ademuri/open-motion-light/test/controller-test.cc

// Copyright 2024 Google LLC
//
// Licensed under the Apache License, Version 2.0 (the "License");
// you may not use this file except in compliance with the License.
// You may obtain a copy of the License at
//
//     http://www.apache.org/licenses/LICENSE-2.0
//
// Unless required by applicable law or agreed to in writing, software
// distributed under the License is distributed on an "AS IS" BASIS,
// WITHOUT WARRANTIES OR CONDITIONS OF ANY KIND, either express or implied.
// See the License for the specific language governing permissions and
// limitations under the License.

#include "controller.h"

#include <gtest/gtest.h>

#include <limits>

#include "fake-power-controller.h"
#include "fake-temperature-sensor.h"
#include "fake-vcnl4020.h"
#include "pb.h"
#include "pins.h"
#include "test-lib.h"
#include "types.h"

// Returns an analog value which approximates the millivolt reading. Note: due
// to precision limits, this is NOT exact.
uint16_t ComputeAnalogValueForMillivolts(uint32_t millivolts) {
  const uint32_t battery_millivolts = Controller::ReadRawBatteryMillivolts();
  EXPECT_LE(millivolts, battery_millivolts);
  return (millivolts * Controller::kAdcConfiguredMaxCount) / battery_millivolts;
}

TEST(ControllerTestFunctionsTest, ComputeAnalogValueForMillivolts) {
  const uint32_t pin = PA0;

  setAnalogRead(AVREF, kFakeVrefintCal * 0.75 / 4);
  const uint16_t battery_millivolts = 4000;
  ASSERT_EQ(Controller::ReadRawBatteryMillivolts(), battery_millivolts);

  const uint16_t value_1000 = ComputeAnalogValueForMillivolts(1000);
  setAnalogRead(pin, value_1000);
  EXPECT_EQ(Controller::ReadAnalogVoltageMillivolts(pin, battery_millivolts),
            1000);

  const uint16_t value_250 = ComputeAnalogValueForMillivolts(250);
  setAnalogRead(pin, value_250);
  EXPECT_EQ(Controller::ReadAnalogVoltageMillivolts(pin, battery_millivolts),
            250);
}

class ControllerTest : public LightTest {
 protected:
  void SetUp() override {
    LightTest::SetUp();
    controller.InitPins();
    setDigitalRead(kPinPowerAuto, true);
    setDigitalRead(kPinPowerOn, true);
    setDigitalRead(kPinBatteryNPowerGood, true);
    setDigitalRead(kPinBatteryStat, false);
    setDigitalRead(kPinMotionSensor, false);
    setDigitalRead(kPin5vDetect, false);
    setAnalogRead(kPinCc1, 0);
    setAnalogRead(kPinCc2, 0);

    // Set to 0 so that the light will always trigger in auto mode.
    vcnl4020.SetAmbient(0);

    // This yields a voltage of 3000 / 0.85 = 3529mV.
    setAnalogRead(AVREF, kFakeVrefintCal * 0.85 / 4);
    ASSERT_EQ(Controller::ReadRawBatteryMillivolts(), 3529);
  }

  FakeTemperatureSensor temperature_sensor;
  FakeVCNL4020 vcnl4020;
  FakePowerController power_controller;
  Controller controller{&temperature_sensor, &vcnl4020, &power_controller};
};

TEST_F(ControllerTest, Initializes) { EXPECT_TRUE(controller.Init()); }

TEST_F(ControllerTest, SetsPowerModeFromSwitch) {
  // These pins are inverted
  setDigitalRead(kPinPowerAuto, true);
  setDigitalRead(kPinPowerOn, true);

  ASSERT_TRUE(controller.Init());
  EXPECT_EQ(controller.GetPowerMode(), PowerMode::kOff);

  setDigitalRead(kPinPowerAuto, false);
  controller.Step();
  EXPECT_EQ(controller.GetPowerMode(), PowerMode::kAuto);

  setDigitalRead(kPinPowerOn, false);
  controller.Step();
  advanceMillis(11);
  controller.Step();
  EXPECT_EQ(controller.GetPowerMode(), PowerMode::kOn);

  setDigitalRead(kPinPowerAuto, true);
  advanceMillis(11);
  controller.Step();
  EXPECT_EQ(controller.GetPowerMode(), PowerMode::kOn);

  setDigitalRead(kPinPowerOn, true);
  advanceMillis(11);
  controller.Step();
  EXPECT_EQ(controller.GetPowerMode(), PowerMode::kOff);
}

TEST_F(ControllerTest, UpdatesLedWhenSwitchingModes) {
  setDigitalRead(kPinPowerAuto, true);
  setDigitalRead(kPinPowerOn, true);

  ASSERT_TRUE(controller.Init());
  const uint32_t duty_cycle = controller.GetLedDutyCycle();
  controller.Step();
  EXPECT_EQ(getAnalogWrite(kPinWhiteLed), 0);

  setDigitalRead(kPinPowerAuto, false);
  controller.Step();
  EXPECT_EQ(getAnalogWrite(kPinWhiteLed), duty_cycle);

  setDigitalRead(kPinPowerOn, false);
  advanceMillis(11);
  controller.Step();
  EXPECT_EQ(getAnalogWrite(kPinWhiteLed), duty_cycle);

  setDigitalRead(kPinPowerAuto, true);
  setDigitalRead(kPinPowerOn, true);
  advanceMillis(11);
  controller.Step();
  EXPECT_EQ(getAnalogWrite(kPinWhiteLed), 0);

  setDigitalRead(kPinMotionSensor, true);
  advanceMillis(11);
  controller.Step();
  EXPECT_EQ(getAnalogWrite(kPinWhiteLed), 0);

  setDigitalRead(kPinPowerAuto, false);
  setDigitalRead(kPinMotionSensor, false);
  advanceMillis(100);
  controller.Step();
  EXPECT_EQ(getAnalogWrite(kPinWhiteLed), duty_cycle)
      << "Switching to auto should turn on light";

  setDigitalRead(kPinPowerOn, false);
  advanceMillis(11);
  controller.Step();
  EXPECT_EQ(getAnalogWrite(kPinWhiteLed), duty_cycle);

  setDigitalRead(kPinPowerOn, true);
  advanceMillis(11);
  controller.Step();
  EXPECT_EQ(getAnalogWrite(kPinWhiteLed), duty_cycle);
}

TEST_F(ControllerTest, DebouncePowerMode) {
  setDigitalRead(kPinPowerAuto, true);
  setDigitalRead(kPinPowerOn, true);

  ASSERT_TRUE(controller.Init());
  ASSERT_EQ(controller.GetPowerMode(), PowerMode::kOff);

  setDigitalRead(kPinPowerAuto, false);
  controller.Step();
  ASSERT_EQ(controller.GetPowerMode(), PowerMode::kAuto);

  setDigitalRead(kPinPowerOn, false);
  controller.Step();
  EXPECT_EQ(controller.GetPowerMode(), PowerMode::kAuto);
  advanceMillis(10);
  controller.Step();
  EXPECT_EQ(controller.GetPowerMode(), PowerMode::kAuto);
  advanceMillis(1);
  controller.Step();
  EXPECT_EQ(controller.GetPowerMode(), PowerMode::kOn);

  setDigitalRead(kPinPowerOn, true);
  advanceMillis(10);
  controller.Step();
  EXPECT_EQ(controller.GetPowerMode(), PowerMode::kOn);
  advanceMillis(1);
  controller.Step();
  EXPECT_EQ(controller.GetPowerMode(), PowerMode::kAuto);
}

TEST_F(ControllerTest, MotionTriggersLed) {
  setDigitalRead(kPinPowerAuto, true);
  setDigitalRead(kPinPowerOn, true);

  ASSERT_TRUE(controller.Init());
  const uint32_t duty_cycle = controller.GetLedDutyCycle();
  ASSERT_GT(duty_cycle, 0);
  EXPECT_EQ(getAnalogWrite(kPinWhiteLed), 0);
  controller.Step();
  EXPECT_EQ(getAnalogWrite(kPinWhiteLed), 0);

  setDigitalRead(kPinPowerAuto, false);
  controller.Step();
  EXPECT_EQ(getAnalogWrite(kPinWhiteLed), duty_cycle);
  advanceMillis(controller.GetMotionTimeoutSeconds() * 1000);
  controller.Step();
  EXPECT_EQ(getAnalogWrite(kPinWhiteLed), duty_cycle);
  advanceMillis(10);
  controller.Step();
  EXPECT_EQ(getAnalogWrite(kPinWhiteLed), 0);

  setDigitalRead(kPinMotionSensor, true);
  controller.Step();
  EXPECT_EQ(getAnalogWrite(kPinWhiteLed), 0);
  advanceMillis(Controller::kMotionPulseLengthMs + 10);
  controller.Step();
  EXPECT_EQ(getAnalogWrite(kPinWhiteLed), duty_cycle);
  setDigitalRead(kPinMotionSensor, false);

  advanceMillis(10);
  controller.Step();
  EXPECT_EQ(getAnalogWrite(kPinWhiteLed), duty_cycle);

  advanceMillis(controller.GetMotionTimeoutSeconds() * 1000 - 10);
  controller.Step();
  EXPECT_EQ(getAnalogWrite(kPinWhiteLed), duty_cycle);

  advanceMillis(1);
  controller.Step();
  EXPECT_EQ(getAnalogWrite(kPinWhiteLed), 0);
}

TEST_F(ControllerTest, ContinuedMotionKeepsLedOn) {
  setDigitalRead(kPinPowerAuto, false);
  setDigitalRead(kPinPowerOn, true);
  setDigitalRead(kPinMotionSensor, false);

  ASSERT_TRUE(controller.Init());
  const uint32_t duty_cycle = controller.GetLedDutyCycle();
  ASSERT_GT(duty_cycle, 0);
  EXPECT_EQ(getAnalogWrite(kPinWhiteLed), 0);
  controller.Step();
  EXPECT_EQ(getAnalogWrite(kPinWhiteLed), duty_cycle);

  advanceMillis(controller.GetMotionTimeoutSeconds() * 1000 + 10);
  controller.Step();
  EXPECT_EQ(getAnalogWrite(kPinWhiteLed), 0);

  setDigitalRead(kPinMotionSensor, true);
  advanceMillis(Controller::kMotionPulseLengthMs);
  controller.Step();
  EXPECT_EQ(getAnalogWrite(kPinWhiteLed), 0);

  advanceMillis(10);
  controller.Step();
  EXPECT_EQ(getAnalogWrite(kPinWhiteLed), duty_cycle);
  setDigitalRead(kPinMotionSensor, false);

  advanceMillis(10);
  controller.Step();
  EXPECT_EQ(getAnalogWrite(kPinWhiteLed), duty_cycle);

  advanceMillis(controller.GetMotionTimeoutSeconds() * 1000 - 20);
  controller.Step();
  EXPECT_EQ(getAnalogWrite(kPinWhiteLed), duty_cycle);

  setDigitalRead(kPinMotionSensor, true);
  advanceMillis(1);
  controller.Step();
  EXPECT_EQ(getAnalogWrite(kPinWhiteLed), duty_cycle);
  advanceMillis(controller.GetMotionTimeoutSeconds() * 1000 * 10);
  controller.Step();
  EXPECT_EQ(getAnalogWrite(kPinWhiteLed), duty_cycle);

  setDigitalRead(kPinMotionSensor, false);
  advanceMillis(controller.GetMotionTimeoutSeconds() * 1000);
  controller.Step();
  EXPECT_EQ(getAnalogWrite(kPinWhiteLed), duty_cycle);
  advanceMillis(1);
  controller.Step();
  EXPECT_EQ(getAnalogWrite(kPinWhiteLed), 0);
}

TEST_F(ControllerTest, ReadsBatteryVoltage) {
  ASSERT_TRUE(controller.Init());

  setAnalogRead(AVREF, kFakeVrefintCal / 4);
  EXPECT_EQ(Controller::ReadRawBatteryMillivolts(), 3000);

  setAnalogRead(AVREF, kFakeVrefintCal * 0.75 / 4);
  EXPECT_EQ(Controller::ReadRawBatteryMillivolts(), 4000);

  setAnalogRead(AVREF, kFakeVrefintCal * 1.5 / 4);
  EXPECT_EQ(Controller::ReadRawBatteryMillivolts(), 2000);
}

TEST_F(ControllerTest, FiltersBatteryVoltage) {
  setAnalogRead(AVREF, kFakeVrefintCal / 4);

  ASSERT_TRUE(controller.Init());
  ASSERT_EQ(Controller::ReadRawBatteryMillivolts(), 3000);
  EXPECT_EQ(controller.GetFilteredBatteryMillivolts(), 3000);

  advanceMillis(Controller::kBatteryFilterRunIntervalMillis + 1);
  controller.Step();
  EXPECT_EQ(controller.GetFilteredBatteryMillivolts(), 3000);

  advanceMillis(Controller::kBatteryFilterRunIntervalMillis + 1);
  setAnalogRead(AVREF, kFakeVrefintCal * 0.75 / 4);
  ASSERT_EQ(Controller::ReadRawBatteryMillivolts(), 4000);
  controller.Step();
  EXPECT_GE(controller.GetFilteredBatteryMillivolts(), 3000);
  EXPECT_LT(controller.GetFilteredBatteryMillivolts(), 4000);

  for (uint32_t n = 0; n < (256 / Controller::kBatteryFilterAlpha) * 2; n++) {
    advanceMillis(Controller::kBatteryFilterRunIntervalMillis + 1);
    controller.Step();
    EXPECT_GE(controller.GetFilteredBatteryMillivolts(), 3000) << "step " << n;
    EXPECT_LT(controller.GetFilteredBatteryMillivolts(), 4000) << "step " << n;
  }
  EXPECT_GT(controller.GetFilteredBatteryMillivolts(), 3800);
}

TEST_F(ControllerTest, SetsPowerStatus) {
  setDigitalRead(kPinBatteryNPowerGood, true);
  setDigitalRead(kPinBatteryStat, false);
  setAnalogRead(kPinCc1, ComputeAnalogValueForMillivolts(0));

  ASSERT_TRUE(controller.Init());
  EXPECT_EQ(controller.GetPowerStatus(), PowerStatus::kBattery);
  controller.Step();
  EXPECT_EQ(controller.GetPowerStatus(), PowerStatus::kBattery);

  setDigitalRead(kPinBatteryNPowerGood, false);
  controller.Step();
  EXPECT_EQ(controller.GetPowerStatus(), PowerStatus::kCharging);

  setDigitalRead(kPinBatteryStat, true);
  controller.Step();
  EXPECT_EQ(controller.GetPowerStatus(), PowerStatus::kCharged);

  // TODO: add test coverage for charge error, once that functionality is
  // implemented.
}

TEST_F(ControllerTest, UsesHysteresisForBatteryVoltage) {
  setAnalogRead(AVREF, kFakeVrefintCal * 1.5 / 4);
  ASSERT_EQ(controller.ReadRawBatteryMillivolts(), 2000);

  ASSERT_TRUE(controller.Init());
  EXPECT_EQ(controller.GetPowerStatus(), PowerStatus::kBattery);
  controller.Step();
  ASSERT_EQ(controller.GetFilteredBatteryMillivolts(), 2000);
  EXPECT_EQ(controller.GetPowerStatus(), PowerStatus::kLowBatteryCutoff);

  setAnalogRead(AVREF, kFakeVrefintCal / 1.05 / 4);
  ASSERT_EQ(controller.ReadRawBatteryMillivolts(), 3157);

  for (uint32_t t = 0; t < 100; t++) {
    advanceMillis(100);
    controller.Step();
    EXPECT_EQ(controller.GetPowerStatus(), PowerStatus::kLowBatteryCutoff);
  }

  ASSERT_EQ(controller.GetFilteredBatteryMillivolts(), 3157);
  EXPECT_EQ(controller.GetPowerStatus(), PowerStatus::kLowBatteryCutoff);

  setAnalogRead(AVREF, kFakeVrefintCal / 1.1 / 4);
  ASSERT_EQ(controller.ReadRawBatteryMillivolts(), 3305);

  for (uint32_t t = 0; t < 100; t++) {
    advanceMillis(100);
    controller.Step();
  }
  ASSERT_EQ(controller.GetFilteredBatteryMillivolts(), 3305);
  EXPECT_EQ(controller.GetPowerStatus(), PowerStatus::kBattery);

  setAnalogRead(AVREF, kFakeVrefintCal / 1.05 / 4);
  ASSERT_EQ(controller.ReadRawBatteryMillivolts(), 3157);

  for (uint32_t t = 0; t < 100; t++) {
    advanceMillis(100);
    controller.Step();
    EXPECT_EQ(controller.GetPowerStatus(), PowerStatus::kBattery);
  }

  ASSERT_EQ(controller.GetFilteredBatteryMillivolts(), 3157);
  EXPECT_EQ(controller.GetPowerStatus(), PowerStatus::kBattery);
}

TEST_F(ControllerTest, DetectsLowBatteryVoltage) {
  setDigitalRead(kPinBatteryNPowerGood, true);
  setDigitalRead(kPinBatteryStat, false);

  setAnalogRead(AVREF, kFakeVrefintCal * 1.5 / 4);
  ASSERT_EQ(controller.ReadRawBatteryMillivolts(), 2000);

  ASSERT_TRUE(controller.Init());
  EXPECT_EQ(controller.GetPowerStatus(), PowerStatus::kBattery);
  controller.Step();
  ASSERT_EQ(controller.GetFilteredBatteryMillivolts(), 2000);
  EXPECT_EQ(controller.GetPowerStatus(), PowerStatus::kLowBatteryCutoff);

  setDigitalRead(kPinBatteryNPowerGood, false);
  controller.Step();
  EXPECT_EQ(controller.GetPowerStatus(),
            PowerStatus::kLowBatteryCutoffCharging);

  setDigitalRead(kPinBatteryStat, true);
  controller.Step();
  EXPECT_EQ(controller.GetPowerStatus(), PowerStatus::kLowBatteryCutoff);
}

TEST_F(ControllerTest, DoesntTurnOnLedWhenBatteryLow) {
  setAnalogRead(AVREF, kFakeVrefintCal * 1.5 / 4);
  ASSERT_EQ(controller.ReadRawBatteryMillivolts(), 2000);

  ASSERT_TRUE(controller.Init());
  ASSERT_EQ(controller.GetPowerStatus(), PowerStatus::kBattery);
  controller.Step();
  ASSERT_EQ(controller.GetFilteredBatteryMillivolts(), 2000);
  ASSERT_EQ(controller.GetPowerStatus(), PowerStatus::kLowBatteryCutoff);

  setDigitalRead(kPinPowerOn, LOW);
  advanceMillis(100);
  controller.Step();
  EXPECT_EQ(controller.GetPowerMode(), PowerMode::kOn);
  EXPECT_EQ(getDigitalWrite(kPinWhiteLed), 0);
  EXPECT_EQ(getAnalogWrite(kPinBatteryLed1), 0);
  EXPECT_EQ(getAnalogWrite(kPinBatteryLed2), 0);
  EXPECT_EQ(getAnalogWrite(kPinBatteryLed3), 0);

  setDigitalRead(kPinPowerOn, HIGH);
  setDigitalRead(kPinPowerAuto, LOW);
  advanceMillis(100);
  controller.Step();
  EXPECT_EQ(controller.GetPowerMode(), PowerMode::kAuto);
  EXPECT_EQ(getDigitalWrite(kPinWhiteLed), 0);
  EXPECT_EQ(getAnalogWrite(kPinBatteryLed1), 0);
  EXPECT_EQ(getAnalogWrite(kPinBatteryLed2), 0);
  EXPECT_EQ(getAnalogWrite(kPinBatteryLed3), 0);

  setAnalogRead(kPinCc1, ComputeAnalogValueForMillivolts(1800));
  setDigitalRead(kPinBatteryNPowerGood, false);
  setDigitalRead(kPinBatteryStat, false);
  controller.Step();
  ASSERT_EQ(controller.GetUSBStatus(), USBStatus::kUSB3_0);
  ASSERT_EQ(controller.GetPowerStatus(),
            PowerStatus::kLowBatteryCutoffCharging);
  EXPECT_EQ(getDigitalWrite(kPinWhiteLed), 0);
}

TEST_F(ControllerTest, TurnsOffLedWhenBatteryLow) {
  ASSERT_TRUE(controller.Init());
  ASSERT_EQ(controller.GetUSBStatus(), USBStatus::kNoConnection);
  ASSERT_EQ(controller.GetPowerStatus(), PowerStatus::kBattery);
  controller.Step();
  ASSERT_GT(controller.GetFilteredBatteryMillivolts(),
            Controller::kBatteryVoltage1);
  ASSERT_EQ(controller.GetUSBStatus(), USBStatus::kNoConnection);
  ASSERT_EQ(controller.GetPowerStatus(), PowerStatus::kBattery);

  setDigitalRead(kPinPowerOn, LOW);
  advanceMillis(100);
  controller.Step();
  EXPECT_EQ(controller.GetPowerMode(), PowerMode::kOn);
  EXPECT_EQ(getAnalogWrite(kPinWhiteLed), controller.GetLedDutyCycle());
  EXPECT_EQ(getAnalogWrite(kPinBatteryLed1),
            Controller::kBatteryLedActiveBrightness);
  EXPECT_EQ(getAnalogWrite(kPinBatteryLed2),
            Controller::kBatteryLedActiveBrightness);
  EXPECT_EQ(getAnalogWrite(kPinBatteryLed3),
            Controller::kBatteryLedActiveBrightness);

  setAnalogRead(AVREF, kFakeVrefintCal * 1.5 / 4);
  ASSERT_EQ(controller.ReadRawBatteryMillivolts(), 2000);

  for (uint32_t t = 0; t < 10; t++) {
    advanceMillis(100);
    controller.Step();
  }

  ASSERT_LT(controller.GetFilteredBatteryMillivolts(),
            Controller::kBatteryVoltage0);
  EXPECT_EQ(controller.GetPowerStatus(), PowerStatus::kLowBatteryCutoff);
  EXPECT_EQ(controller.GetPowerMode(), PowerMode::kOn);
  EXPECT_EQ(getAnalogWrite(kPinWhiteLed), 0);
  EXPECT_EQ(getAnalogWrite(kPinBatteryLed1), 0);
  EXPECT_EQ(getAnalogWrite(kPinBatteryLed2), 0);
  EXPECT_EQ(getAnalogWrite(kPinBatteryLed3), 0);
}

TEST_F(ControllerTest, SetsUSBStatus) {
  // Battery voltage should be max ~3.6V.
  setAnalogRead(AVREF, kFakeVrefintCal * 0.8 / 4);
  ASSERT_EQ(Controller::ReadRawBatteryMillivolts(), 3750);

  const uint16_t vusb_min = ComputeAnalogValueForMillivolts(200);
  const uint16_t vusb_max = ComputeAnalogValueForMillivolts(610);
  const uint16_t v1_5_min = ComputeAnalogValueForMillivolts(700);
  const uint16_t v1_5_max = ComputeAnalogValueForMillivolts(1160);
  const uint16_t v3_0_min = ComputeAnalogValueForMillivolts(1310);
  const uint16_t v3_0_max = ComputeAnalogValueForMillivolts(2040);
  setAnalogRead(kPinCc1, 0);
  setAnalogRead(kPinCc2, 0);

  ASSERT_TRUE(controller.Init());
  EXPECT_EQ(controller.GetUSBStatus(), USBStatus::kNoConnection);
  controller.Step();
  EXPECT_EQ(controller.GetUSBStatus(), USBStatus::kNoConnection);
  EXPECT_FALSE(getDigitalWrite(kPinChargeHighCurrentEnable));

  setAnalogRead(kPinCc1, vusb_min - 1);
  controller.Step();
  EXPECT_EQ(controller.GetUSBStatus(), USBStatus::kNoConnection);
  EXPECT_FALSE(getDigitalWrite(kPinChargeHighCurrentEnable));

  setAnalogRead(kPinCc1, vusb_min + 1);
  controller.Step();
  EXPECT_EQ(controller.GetUSBStatus(), USBStatus::kStandardUsb);
  EXPECT_FALSE(getDigitalWrite(kPinChargeHighCurrentEnable));

  setAnalogRead(kPinCc1, vusb_max - 1);
  controller.Step();
  EXPECT_EQ(controller.GetUSBStatus(), USBStatus::kStandardUsb);
  EXPECT_FALSE(getDigitalWrite(kPinChargeHighCurrentEnable));

  setAnalogRead(kPinCc1, v1_5_min + 1);
  controller.Step();
  EXPECT_EQ(controller.GetUSBStatus(), USBStatus::kUSB1_5);
  EXPECT_TRUE(getDigitalWrite(kPinChargeHighCurrentEnable));

  setAnalogRead(kPinCc1, v1_5_max - 1);
  controller.Step();
  EXPECT_EQ(controller.GetUSBStatus(), USBStatus::kUSB1_5);
  EXPECT_TRUE(getDigitalWrite(kPinChargeHighCurrentEnable));

  setAnalogRead(kPinCc1, v3_0_min + 1);
  controller.Step();
  EXPECT_EQ(controller.GetUSBStatus(), USBStatus::kUSB3_0);
  EXPECT_TRUE(getDigitalWrite(kPinChargeHighCurrentEnable));

  setAnalogRead(kPinCc1, v3_0_max - 1);
  controller.Step();
  EXPECT_EQ(controller.GetUSBStatus(), USBStatus::kUSB3_0);
  EXPECT_TRUE(getDigitalWrite(kPinChargeHighCurrentEnable));
}

TEST_F(ControllerTest, SetsUSBFromCC1AndCC2) {
  // Battery voltage should be max ~3.6V.
  setAnalogRead(AVREF, kFakeVrefintCal * 0.8 / 4);
  ASSERT_EQ(Controller::ReadRawBatteryMillivolts(), 3750);

  const uint16_t vusb_max = ComputeAnalogValueForMillivolts(610);
  const uint16_t v1_5_min = ComputeAnalogValueForMillivolts(700);
  setAnalogRead(kPinCc1, 0);
  setAnalogRead(kPinCc2, 0);

  ASSERT_TRUE(controller.Init());
  controller.Step();
  ASSERT_EQ(controller.GetUSBStatus(), USBStatus::kNoConnection);
  EXPECT_FALSE(getDigitalWrite(kPinChargeHighCurrentEnable));

  setAnalogRead(kPinCc1, v1_5_min + 1);
  controller.Step();
  EXPECT_EQ(controller.GetUSBStatus(), USBStatus::kUSB1_5);
  EXPECT_TRUE(getDigitalWrite(kPinChargeHighCurrentEnable));

  setAnalogRead(kPinCc1, 0);
  setAnalogRead(kPinCc2, v1_5_min + 1);
  controller.Step();
  EXPECT_EQ(controller.GetUSBStatus(), USBStatus::kUSB1_5);
  EXPECT_TRUE(getDigitalWrite(kPinChargeHighCurrentEnable));

  setAnalogRead(kPinCc1, vusb_max - 1);
  setAnalogRead(kPinCc2, v1_5_min + 1);
  controller.Step();
  EXPECT_EQ(controller.GetUSBStatus(), USBStatus::kUSB1_5);
  EXPECT_TRUE(getDigitalWrite(kPinChargeHighCurrentEnable));
}

TEST_F(ControllerTest, DoesntTurnOnWhenUSBConnected) {
  const uint16_t vusb_max = ComputeAnalogValueForMillivolts(610);
  setAnalogRead(kPinCc1, vusb_max);
  setAnalogRead(kPinCc2, 0);

  ASSERT_TRUE(controller.Init());
  controller.Step();
  ASSERT_EQ(controller.GetUSBStatus(), USBStatus::kStandardUsb);

  setDigitalRead(kPinPowerOn, false);
  controller.Step();
  ASSERT_EQ(controller.GetPowerMode(), PowerMode::kOn);
  EXPECT_EQ(getAnalogWrite(kPinWhiteLed), 0);

  setAnalogRead(kPinCc1, 0);
  controller.Step();
  ASSERT_EQ(controller.GetUSBStatus(), USBStatus::kNoConnection);
  EXPECT_EQ(getAnalogWrite(kPinWhiteLed), controller.GetLedDutyCycle());

  setAnalogRead(kPinCc1, vusb_max);
  controller.Step();
  ASSERT_EQ(controller.GetUSBStatus(), USBStatus::kStandardUsb);
  EXPECT_EQ(getAnalogWrite(kPinWhiteLed), 0);

  setDigitalRead(kPinPowerOn, true);
  setDigitalRead(kPinPowerAuto, false);
  advanceMillis(11);
  controller.Step();
  ASSERT_EQ(controller.GetPowerMode(), PowerMode::kAuto);
  EXPECT_EQ(getAnalogWrite(kPinWhiteLed), 0);

  setAnalogRead(kPinCc1, 0);
  setDigitalRead(kPinMotionSensor, true);
  controller.Step();
  ASSERT_EQ(controller.GetUSBStatus(), USBStatus::kNoConnection);
  EXPECT_EQ(getAnalogWrite(kPinWhiteLed), controller.GetLedDutyCycle());

  setAnalogRead(kPinCc1, vusb_max);
  controller.Step();
  ASSERT_EQ(controller.GetUSBStatus(), USBStatus::kStandardUsb);
  EXPECT_EQ(getAnalogWrite(kPinWhiteLed), 0);
}

TEST_F(ControllerTest, ReadsAnalogVoltage) {
  const uint32_t pin = PA0;
  pinMode(pin, INPUT_ANALOG);

  setAnalogRead(pin, Controller::kAdcConfiguredMaxCount);
  EXPECT_EQ(
      Controller::ReadAnalogVoltageMillivolts(pin, /*battery_millivolts=*/3000),
      3000);

  setAnalogRead(pin, Controller::kAdcConfiguredMaxCount / 2);
  EXPECT_EQ(
      Controller::ReadAnalogVoltageMillivolts(pin, /*battery_millivolts=*/3000),
      1500);
}

std::array<uint32_t, 3> BatteryLeds(uint32_t led1, uint32_t led2,
                                    uint32_t led3) {
  return {led1, led2, led3};
}

std::array<uint32_t, 3> GetBatteryLeds() {
  return BatteryLeds(getAnalogWrite(kPinBatteryLed1),
                     getAnalogWrite(kPinBatteryLed2),
                     getAnalogWrite(kPinBatteryLed3));
}

TEST_F(ControllerTest, DisplaysBatteryVoltage) {
  setDigitalRead(kPinBatteryNPowerGood, true);
  setDigitalRead(kPinBatteryStat, false);

  setAnalogRead(AVREF,
                (kFakeVrefintCal * Controller::kReferenceSupplyMillivolts) /
                    (Controller::kBatteryVoltage1 + 100) / 4);
  ASSERT_GT(controller.ReadRawBatteryMillivolts(),
            Controller::kBatteryVoltage1);
  ASSERT_TRUE(controller.Init());
  EXPECT_EQ(GetBatteryLeds(), BatteryLeds(0, 0, 0));

  setDigitalRead(kPinPowerAuto, false);
  controller.Step();
  ASSERT_EQ(controller.GetPowerMode(), PowerMode::kAuto);
  EXPECT_EQ(GetBatteryLeds(),
            BatteryLeds(Controller::kBatteryLedActiveBrightness,
                        Controller::kBatteryLedActiveBrightness,
                        Controller::kBatteryLedActiveBrightness));

  advanceMillis(Controller::kBatteryLevelDisplayTimeSeconds * 1000 + 10);
  controller.Step();
  EXPECT_EQ(GetBatteryLeds(), BatteryLeds(0, 0, 0));

  // Medium voltage
  setAnalogRead(AVREF,
                (kFakeVrefintCal * Controller::kReferenceSupplyMillivolts) /
                    (Controller::kBatteryVoltage0 + 10) / 4);
  ASSERT_GT(controller.ReadRawBatteryMillivolts(),
            Controller::kBatteryVoltage0);
  ASSERT_LT(controller.ReadRawBatteryMillivolts(),
            Controller::kBatteryVoltage1);
  // Pump the battery voltage filters
  for (uint32_t n = 0; n < 100; n++) {
    advanceMillis(Controller::kBatteryFilterRunIntervalMillis + 1);
    controller.Step();
  }

  setDigitalRead(kPinPowerAuto, true);
  setDigitalRead(kPinPowerOn, false);
  controller.Step();
  ASSERT_EQ(controller.GetPowerMode(), PowerMode::kOn);
  EXPECT_EQ(GetBatteryLeds(),
            BatteryLeds(Controller::kBatteryLedPlaceholderBrightness,
                        Controller::kBatteryLedActiveBrightness,
                        Controller::kBatteryLedActiveBrightness));

  // Low voltage
  setAnalogRead(AVREF,
                (kFakeVrefintCal * Controller::kReferenceSupplyMillivolts) /
                    (Controller::kBatteryVoltage0 - 10) / 4);
  ASSERT_LT(controller.ReadRawBatteryMillivolts(),
            Controller::kBatteryVoltage0);
  // Pump the battery voltage filters
  for (uint32_t n = 0; n < 100; n++) {
    advanceMillis(Controller::kBatteryFilterRunIntervalMillis + 1);
    controller.Step();
  }

  setDigitalRead(kPinPowerAuto, false);
  setDigitalRead(kPinPowerOn, true);
  controller.Step();
  ASSERT_EQ(controller.GetPowerMode(), PowerMode::kAuto);
  EXPECT_EQ(GetBatteryLeds(),
            BatteryLeds(Controller::kBatteryLedPlaceholderBrightness,
                        Controller::kBatteryLedPlaceholderBrightness,
                        Controller::kBatteryLedActiveBrightness));
}

TEST_F(ControllerTest, AmbientAndProximitySensorsWork) {
  ASSERT_TRUE(controller.Init());

  vcnl4020.SetAmbient(500);
  EXPECT_EQ(controller.ReadAmbientLight(), 500);

  vcnl4020.SetProximity(600);
  EXPECT_EQ(controller.ReadProximity(), 600);
}

TEST_F(ControllerTest, Sleeps) {
  ASSERT_TRUE(controller.Init());
  EXPECT_EQ(controller.GetPowerMode(), PowerMode::kOff);
  EXPECT_EQ(power_controller.GetSleep(), 0);

  uint32_t sleep_interval = controller.GetSleepInterval();
  ASSERT_NE(sleep_interval, 0);

  advanceMillis(Controller::kSleepLockoutMs + 1);
  controller.Step();
  EXPECT_EQ(power_controller.GetSleep(), sleep_interval);
}

TEST_F(ControllerTest, NoSleepWhenCharging) {
  ASSERT_TRUE(controller.Init());
  EXPECT_EQ(controller.GetPowerMode(), PowerMode::kOff);
  EXPECT_EQ(power_controller.GetSleep(), 0);

  setDigitalRead(kPinBatteryNPowerGood, false);
  controller.Step();

  uint32_t sleep_interval = controller.GetSleepInterval();
  ASSERT_NE(sleep_interval, 0);

  advanceMillis(Controller::kSleepLockoutMs + 1);
  controller.Step();
  EXPECT_EQ(power_controller.GetSleep(), 0);

  advanceMillis(Controller::kSleepLockoutMs * 5);
  controller.Step();
  EXPECT_EQ(power_controller.GetSleep(), 0);

  setDigitalRead(kPinBatteryNPowerGood, true);
  advanceMillis(Controller::kSleepLockoutMs + 1);
  controller.Step();
  EXPECT_EQ(power_controller.GetSleep(), sleep_interval);
}

TEST_F(ControllerTest, NoSleepWhenUsbConnected) {
  ASSERT_TRUE(controller.Init());
  EXPECT_EQ(controller.GetPowerMode(), PowerMode::kOff);
  EXPECT_EQ(power_controller.GetSleep(), 0);

  setAnalogRead(kPinCc1, ComputeAnalogValueForMillivolts(1800));
  controller.Step();

  uint32_t sleep_interval = controller.GetSleepInterval();
  ASSERT_NE(sleep_interval, 0);

  advanceMillis(Controller::kSleepLockoutMs + 1);
  controller.Step();
  EXPECT_EQ(power_controller.GetSleep(), 0);

  advanceMillis(Controller::kSleepLockoutMs * 5);
  controller.Step();
  EXPECT_EQ(power_controller.GetSleep(), 0);

  setAnalogRead(kPinCc1, ComputeAnalogValueForMillivolts(0));
  advanceMillis(Controller::kSleepLockoutMs + 1);
  controller.Step();
  EXPECT_EQ(power_controller.GetSleep(), sleep_interval);
}

TEST_F(ControllerTest, NoSleepWhen5vConnected) {
  ASSERT_TRUE(controller.Init());
  EXPECT_EQ(controller.GetPowerMode(), PowerMode::kOff);
  EXPECT_EQ(power_controller.GetSleep(), 0);

  setDigitalRead(kPin5vDetect, true);
  controller.Step();

  uint32_t sleep_interval = controller.GetSleepInterval();
  ASSERT_NE(sleep_interval, 0);

  advanceMillis(Controller::kSleepLockoutMs + 1);
  controller.Step();
  EXPECT_EQ(power_controller.GetSleep(), 0);

  advanceMillis(Controller::kSleepLockoutMs * 5);
  controller.Step();
  EXPECT_EQ(power_controller.GetSleep(), 0);

  setDigitalRead(kPin5vDetect, false);
  advanceMillis(Controller::kSleepLockoutMs + 1);
  controller.Step();
  EXPECT_EQ(power_controller.GetSleep(), sleep_interval);
}

TEST_F(ControllerTest, EnablesLightSensorPeriodicMeasurements) {
  controller.SetConfig(
      {brightnessMode : BrightnessMode::BRIGHTNESS_MODE_ON_WHEN_BELOW});
  ASSERT_TRUE(controller.Init());
  controller.Step();
  ASSERT_EQ(controller.GetPowerMode(), PowerMode::kOff);
  EXPECT_EQ(vcnl4020.GetPeriodicAmbient(), false);

  setDigitalRead(kPinPowerAuto, false);
  advanceMillis(20);
  controller.Step();
  EXPECT_EQ(controller.GetPowerMode(), PowerMode::kAuto);
  EXPECT_EQ(vcnl4020.GetPeriodicAmbient(), true);

  setDigitalRead(kPinPowerAuto, true);
  setDigitalRead(kPinPowerOn, false);
  advanceMillis(20);
  controller.Step();
  EXPECT_EQ(controller.GetPowerMode(), PowerMode::kOn);
  EXPECT_EQ(vcnl4020.GetPeriodicAmbient(), false);

  setDigitalRead(kPinPowerOn, true);
  advanceMillis(20);
  controller.Step();
  EXPECT_EQ(controller.GetPowerMode(), PowerMode::kOff);
  EXPECT_EQ(vcnl4020.GetPeriodicAmbient(), false);
}

TEST_F(ControllerTest,
       DisablesLightSensorPeriodicMeasurementsWhenBrightnessModeDisabled) {
  controller.SetConfig(
      {brightnessMode : BrightnessMode::BRIGHTNESS_MODE_ON_WHEN_BELOW});
  ASSERT_TRUE(controller.Init());
  controller.Step();
  ASSERT_EQ(controller.GetPowerMode(), PowerMode::kOff);
  EXPECT_EQ(vcnl4020.GetPeriodicAmbient(), false);

  setDigitalRead(kPinPowerAuto, false);
  advanceMillis(20);
  controller.Step();
  EXPECT_EQ(controller.GetPowerMode(), PowerMode::kAuto);
  EXPECT_EQ(vcnl4020.GetPeriodicAmbient(), true);

  controller.SetConfig(
      {brightnessMode : BrightnessMode::BRIGHTNESS_MODE_DISABLED});
  advanceMillis(20);
  controller.Step();
  EXPECT_EQ(controller.GetPowerMode(), PowerMode::kAuto);
  EXPECT_EQ(vcnl4020.GetPeriodicAmbient(), true);
}

TEST_F(ControllerTest, UsesAmbientLightForAutoModeBrightnessModeOnWhenBelow) {
  controller.SetConfig({
    brightnessMode : BrightnessMode::BRIGHTNESS_MODE_ON_WHEN_BELOW,
    autoBrightnessThreshold : 100
  });
  setDigitalRead(kPinPowerAuto, false);
  vcnl4020.SetAmbient(101);
  ASSERT_TRUE(controller.Init());
  controller.Step();
  ASSERT_EQ(controller.GetPowerMode(), PowerMode::kAuto);
  EXPECT_EQ(vcnl4020.GetPeriodicAmbient(), true);
  EXPECT_EQ(getAnalogWrite(kPinWhiteLed), controller.GetLedDutyCycle());

  advanceMillis(controller.GetMotionTimeoutSeconds() * 1000 + 10);
  controller.Step();
  EXPECT_EQ(controller.GetPowerMode(), PowerMode::kAuto);
  EXPECT_EQ(getAnalogWrite(kPinWhiteLed), 0);
  advanceMillis(Controller::kMotionPulseLengthMs + 10);
  controller.Step();
  EXPECT_EQ(controller.GetPowerMode(), PowerMode::kAuto);
  EXPECT_EQ(getAnalogWrite(kPinWhiteLed), 0);

  setDigitalRead(kPinMotionSensor, true);
  advanceMillis(Controller::kBrightnessIgnorePeriodMs + 10);
  controller.Step();
  EXPECT_EQ(getAnalogWrite(kPinWhiteLed), 0);

  setDigitalRead(kPinMotionSensor, false);
  advanceMillis(10);
  controller.Step();
  EXPECT_EQ(getAnalogWrite(kPinWhiteLed), 0);

  vcnl4020.SetAmbient(99);
  setDigitalRead(kPinMotionSensor, true);
  advanceMillis(10);
  controller.Step();
  EXPECT_EQ(getAnalogWrite(kPinWhiteLed), controller.GetLedDutyCycle());

  vcnl4020.SetAmbient(101);
  advanceMillis(controller.GetMotionTimeoutSeconds() * 1000 + 10);
  controller.Step();
  EXPECT_EQ(getAnalogWrite(kPinWhiteLed), controller.GetLedDutyCycle());

  setDigitalRead(kPinMotionSensor, false);
  advanceMillis(controller.GetMotionTimeoutSeconds() * 1000 + 10);
  controller.Step();
  EXPECT_EQ(getAnalogWrite(kPinWhiteLed), 0);
}

TEST_F(ControllerTest, RetriggersCorrectlyWithBrightnessInAutoMode) {
  controller.SetConfig({
    brightnessMode : BrightnessMode::BRIGHTNESS_MODE_ON_WHEN_BELOW,
    autoBrightnessThreshold : 100
  });
  setDigitalRead(kPinPowerAuto, false);
  ASSERT_TRUE(controller.Init());
  controller.Step();
  ASSERT_EQ(controller.GetPowerMode(), PowerMode::kAuto);
  EXPECT_EQ(getAnalogWrite(kPinWhiteLed), controller.GetLedDutyCycle());

  advanceMillis(controller.GetMotionTimeoutSeconds() * 1000 - 10);
  setDigitalRead(kPinMotionSensor, true);
  vcnl4020.SetAmbient(1000);
  controller.Step();
  EXPECT_EQ(getAnalogWrite(kPinWhiteLed), controller.GetLedDutyCycle());

  setDigitalRead(kPinMotionSensor, false);
  advanceMillis(20);
  controller.Step();
  EXPECT_EQ(getAnalogWrite(kPinWhiteLed), controller.GetLedDutyCycle());

  advanceMillis(controller.GetMotionTimeoutSeconds() * 1000 + 10);
  controller.Step();
  EXPECT_EQ(getAnalogWrite(kPinWhiteLed), 0);

  setDigitalRead(kPinMotionSensor, true);
  if (Controller::kMotionPulseLengthMs <
      Controller::kBrightnessIgnorePeriodMs) {
    advanceMillis(Controller::kBrightnessIgnorePeriodMs - 20);
    controller.Step();
    EXPECT_EQ(getAnalogWrite(kPinWhiteLed), controller.GetLedDutyCycle());

    setDigitalRead(kPinMotionSensor, false);
    advanceMillis(20);
    controller.Step();
    EXPECT_EQ(getAnalogWrite(kPinWhiteLed), controller.GetLedDutyCycle());
  }

  advanceMillis(controller.GetMotionTimeoutSeconds() * 1000 + 10);
  controller.Step();
  EXPECT_EQ(getAnalogWrite(kPinWhiteLed), 0);

  setDigitalRead(kPinMotionSensor, true);
  advanceMillis(Controller::kBrightnessIgnorePeriodMs + 20);
  controller.Step();
  EXPECT_EQ(getAnalogWrite(kPinWhiteLed), 0);
}

TEST_F(ControllerTest, IgnoresAmbientLightForAutoModeBrightnessDisabled) {
  controller.SetConfig(
      {brightnessMode : BrightnessMode::BRIGHTNESS_MODE_DISABLED});
  setDigitalRead(kPinPowerAuto, false);
  vcnl4020.SetAmbient(0xFFFF);
  ASSERT_TRUE(controller.Init());
  controller.Step();
  ASSERT_EQ(controller.GetPowerMode(), PowerMode::kAuto);
  EXPECT_EQ(vcnl4020.GetPeriodicAmbient(), false);
  EXPECT_EQ(getAnalogWrite(kPinWhiteLed), controller.GetLedDutyCycle());

  advanceMillis(controller.GetMotionTimeoutSeconds() * 1000 + 10);
  controller.Step();
  EXPECT_EQ(getAnalogWrite(kPinWhiteLed), 0);
  advanceMillis(Controller::kMotionPulseLengthMs + 10);
  controller.Step();
  EXPECT_EQ(getAnalogWrite(kPinWhiteLed), 0);

  setDigitalRead(kPinMotionSensor, true);
  advanceMillis(10);
  controller.Step();
  EXPECT_EQ(getAnalogWrite(kPinWhiteLed), controller.GetLedDutyCycle());

  setDigitalRead(kPinMotionSensor, false);
  advanceMillis(controller.GetMotionTimeoutSeconds() * 1000 + 10);
  controller.Step();
  EXPECT_EQ(getAnalogWrite(kPinWhiteLed), 0);

  advanceMillis(Controller::kMotionPulseLengthMs + 10);
  controller.Step();
  EXPECT_EQ(getAnalogWrite(kPinWhiteLed), 0);

  vcnl4020.SetAmbient(0);
  setDigitalRead(kPinMotionSensor, true);
  advanceMillis(10);
  controller.Step();
  EXPECT_EQ(getAnalogWrite(kPinWhiteLed), controller.GetLedDutyCycle());
}

TEST_F(ControllerTest, EnablesProxSensorForProximityToggleMode) {
  controller.SetConfig({
    proximity_mode : ProximityMode::PROXIMITY_MODE_TOGGLE,
  });
  ASSERT_TRUE(controller.Init());
  controller.Step();
  EXPECT_EQ(vcnl4020.GetPeriodicProximity(), false);

  setDigitalRead(kPinPowerAuto, false);
  controller.Step();
  ASSERT_EQ(controller.GetPowerMode(), PowerMode::kAuto);
  EXPECT_EQ(getAnalogWrite(kPinWhiteLed), controller.GetLedDutyCycle());
  EXPECT_EQ(vcnl4020.GetPeriodicProximity(), true);

  advanceMillis(Controller::kMotionProximityPeriodMs - 10);
  controller.Step();
  EXPECT_EQ(vcnl4020.GetPeriodicProximity(), true);

  advanceMillis(20);
  controller.Step();
  EXPECT_EQ(vcnl4020.GetPeriodicProximity(), false);

  advanceMillis(controller.GetMotionTimeoutSeconds() * 1000);
  controller.Step();

  setDigitalRead(kPinMotionSensor, true);
  advanceMillis(10);
  controller.Step();
  EXPECT_EQ(vcnl4020.GetPeriodicProximity(), true);
}

TEST_F(ControllerTest, TogglesLedInProximityModeToggle) {
  controller.SetConfig({
    proximity_mode : ProximityMode::PROXIMITY_MODE_TOGGLE,
    proximity_threshold : 5,
  });
  ASSERT_TRUE(controller.Init());
  vcnl4020.SetProximity(100);
  vcnl4020.SetProximityReady();
  controller.Step();
  EXPECT_EQ(vcnl4020.GetPeriodicProximity(), false);

  setDigitalRead(kPinPowerAuto, false);
  controller.Step();
  EXPECT_EQ(controller.GetPowerMode(), PowerMode::kAuto);
  ASSERT_EQ(getAnalogWrite(kPinWhiteLed), controller.GetLedDutyCycle());
  ASSERT_EQ(vcnl4020.GetPeriodicProximity(), true);

  vcnl4020.SetProximity(101);
  vcnl4020.SetProximityReady();
  advanceMillis(10);
  controller.Step();
  EXPECT_EQ(controller.GetPowerMode(), PowerMode::kAuto);

  vcnl4020.SetProximity(107);
  vcnl4020.SetProximityReady();
  advanceMillis(10);
  controller.Step();
  EXPECT_EQ(controller.GetPowerMode(), PowerMode::kToggled);
  EXPECT_EQ(getAnalogWrite(kPinWhiteLed), controller.GetLedDutyCycle());

  vcnl4020.SetProximity(107);
  vcnl4020.SetProximityReady();
  advanceMillis(controller.GetMotionTimeoutSeconds() * 1000 + 10);
  controller.Step();
  EXPECT_EQ(getAnalogWrite(kPinWhiteLed), controller.GetLedDutyCycle());
  EXPECT_EQ(controller.GetPowerMode(), PowerMode::kToggled);

  advanceMillis(controller.GetMotionTimeoutSeconds() * 1000 + 10);
  controller.Step();
  EXPECT_EQ(getAnalogWrite(kPinWhiteLed), controller.GetLedDutyCycle());
  EXPECT_EQ(controller.GetPowerMode(), PowerMode::kToggled);

  EXPECT_EQ(vcnl4020.GetPeriodicProximity(), true);
  vcnl4020.SetProximity(100);
  vcnl4020.SetProximityReady();
  advanceMillis(10);
  controller.Step();
  EXPECT_EQ(controller.GetPowerMode(), PowerMode::kAuto);
  EXPECT_EQ(getAnalogWrite(kPinWhiteLed), 0);
}

TEST_F(ControllerTest, HandlesMillisRollover) {
  pinMode(kPinPowerOn, OUTPUT);
  pinMode(kPinPowerAuto, OUTPUT);

  setMillis(std::numeric_limits<uint32_t>::max() - 1000);
  setDigitalRead(kPinPowerAuto, true);
  setDigitalRead(kPinPowerOn, true);

  ASSERT_TRUE(controller.Init());
  const uint32_t duty_cycle = controller.GetLedDutyCycle();
  controller.Step();
  EXPECT_EQ(controller.GetPowerMode(), PowerMode::kOff);
  EXPECT_EQ(getAnalogWrite(kPinWhiteLed), 0);

  setDigitalRead(kPinPowerOn, false);
  advanceMillis(100);
  controller.Step();
  EXPECT_EQ(controller.GetPowerMode(), PowerMode::kOn);
  EXPECT_EQ(getAnalogWrite(kPinWhiteLed), duty_cycle);

  setDigitalRead(kPinPowerOn, true);
  advanceMillis(100);
  controller.Step();
  EXPECT_EQ(controller.GetPowerMode(), PowerMode::kOff);
  EXPECT_EQ(getAnalogWrite(kPinWhiteLed), 0);

  setDigitalRead(kPinPowerOn, false);
  setMillis(100);
  controller.Step();
  EXPECT_EQ(controller.GetPowerMode(), PowerMode::kOn);
  EXPECT_EQ(getAnalogWrite(kPinWhiteLed), duty_cycle);

  setDigitalRead(kPinPowerOn, true);
  advanceMillis(100);
  controller.Step();
  EXPECT_EQ(controller.GetPowerMode(), PowerMode::kOff);
  EXPECT_EQ(getAnalogWrite(kPinWhiteLed), 0);
}

TEST_F(ControllerTest, SetsSensitivityPins) {
  ASSERT_TRUE(controller.Init());

  ConfigPb config = *controller.GetConfig();

  // UNSPECIFIED should be the same as ONE
  config.motion_sensitivity =
      MotionSensitivity::MotionSensitivity_MOTION_SENSITIVITY_UNSPECIFIED;
  controller.SetConfig(config);
  EXPECT_EQ(getPinMode(kPinSensitivityLow), INPUT_ANALOG);
  EXPECT_EQ(getPinMode(kPinSensitivityHigh1), INPUT_ANALOG);
  EXPECT_EQ(getPinMode(kPinSensitivityHigh2), INPUT_ANALOG);

  config.motion_sensitivity =
      MotionSensitivity::MotionSensitivity_MOTION_SENSITIVITY_ONE;
  controller.SetConfig(config);
  EXPECT_EQ(getPinMode(kPinSensitivityLow), INPUT_ANALOG);
  EXPECT_EQ(getPinMode(kPinSensitivityHigh1), INPUT_ANALOG);
  EXPECT_EQ(getPinMode(kPinSensitivityHigh2), INPUT_ANALOG);

  config.motion_sensitivity =
      MotionSensitivity::MotionSensitivity_MOTION_SENSITIVITY_TWO;
  controller.SetConfig(config);
  EXPECT_EQ(getPinMode(kPinSensitivityLow), INPUT_ANALOG);
  EXPECT_EQ(getPinMode(kPinSensitivityHigh1), OUTPUT);
  EXPECT_TRUE(getDigitalWrite(kPinSensitivityHigh1));
  EXPECT_EQ(getPinMode(kPinSensitivityHigh2), INPUT_ANALOG);

  config.motion_sensitivity =
      MotionSensitivity::MotionSensitivity_MOTION_SENSITIVITY_THREE;
  controller.SetConfig(config);
  EXPECT_EQ(getPinMode(kPinSensitivityLow), OUTPUT);
  EXPECT_TRUE(getDigitalWrite(kPinSensitivityLow));
  EXPECT_EQ(getPinMode(kPinSensitivityHigh1), OUTPUT);
  EXPECT_TRUE(getDigitalWrite(kPinSensitivityHigh1));
  EXPECT_EQ(getPinMode(kPinSensitivityHigh2), OUTPUT);
  EXPECT_TRUE(getDigitalWrite(kPinSensitivityHigh2));
}
